Frapais/Sprig-C6/PCB/DSCF2212.jpg

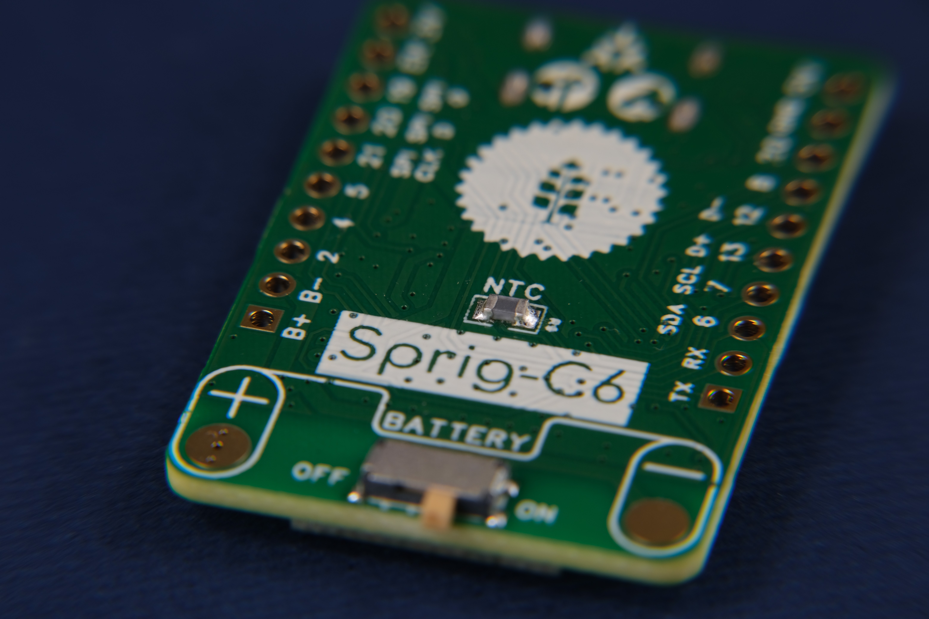
PCB/DSCF2212.jpg
